MakersAsylumIndia/IS2026_SU_Team13_Vector/Documentation/Block Diagram.jpeg

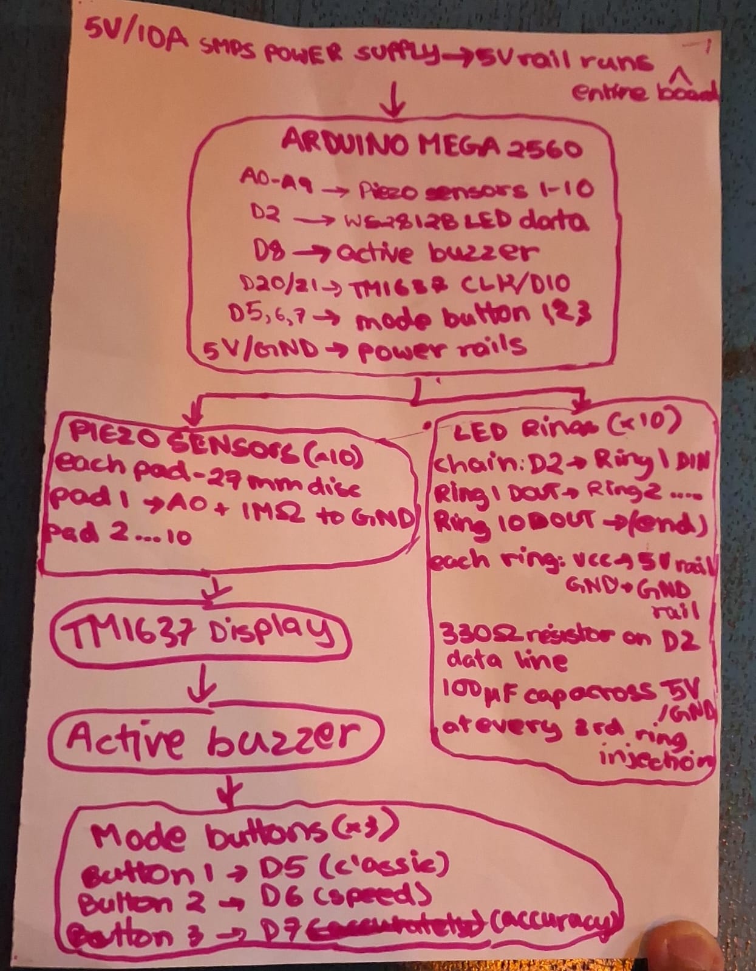
Documentation/Block Diagram.jpeg
