MakersAsylumIndia/IS2026_SU_Team13_Vector/Documentation/Project_Ideation_Sketch.jpeg

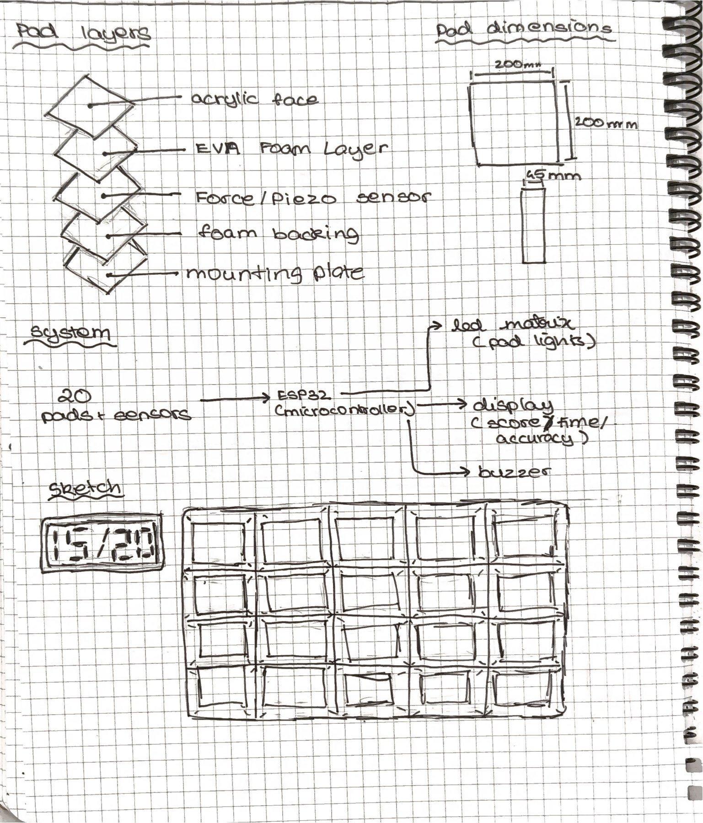
Documentation/Project_Ideation_Sketch.jpeg
