MakersAsylumIndia/IS2026_SU_Team13_Vector/Photos_Videos/Images/shared image (18).jpeg

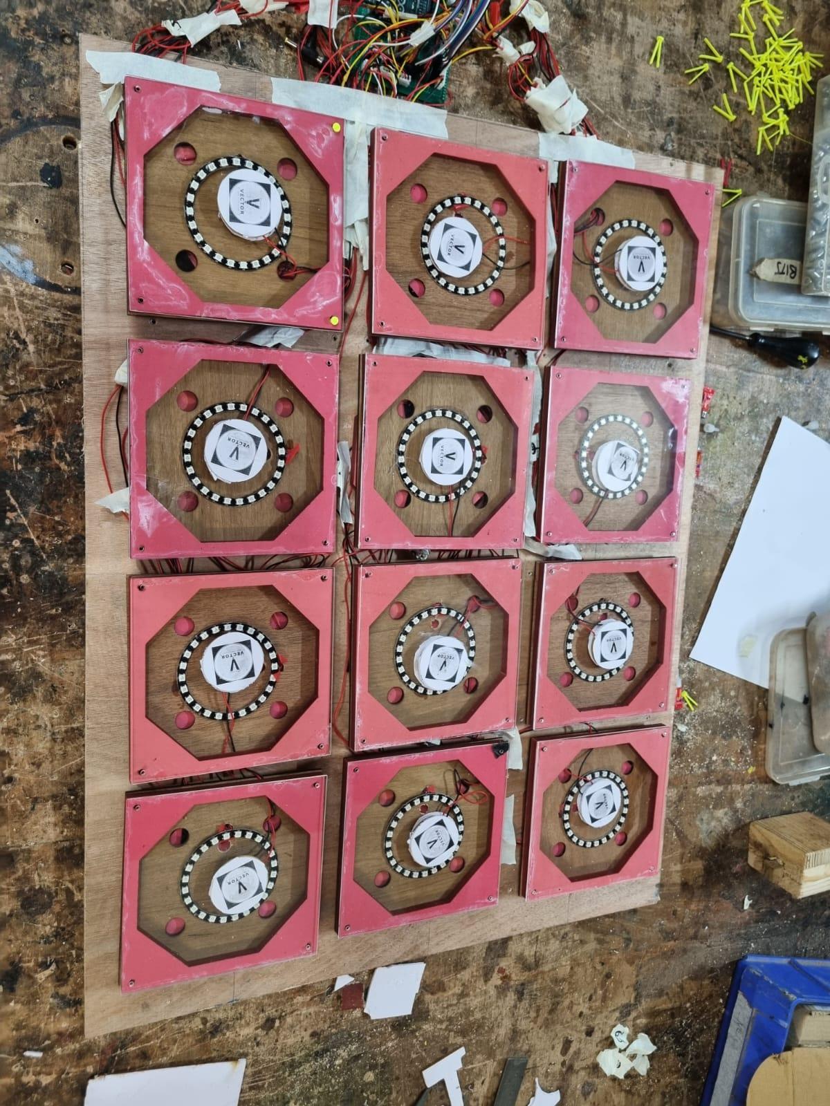
Photos_Videos/Images/shared image (18).jpeg
