MakersAsylumIndia/IS2026_SU_Team13_Vector/Photos_Videos/Images/Team_Vector_01.jpg

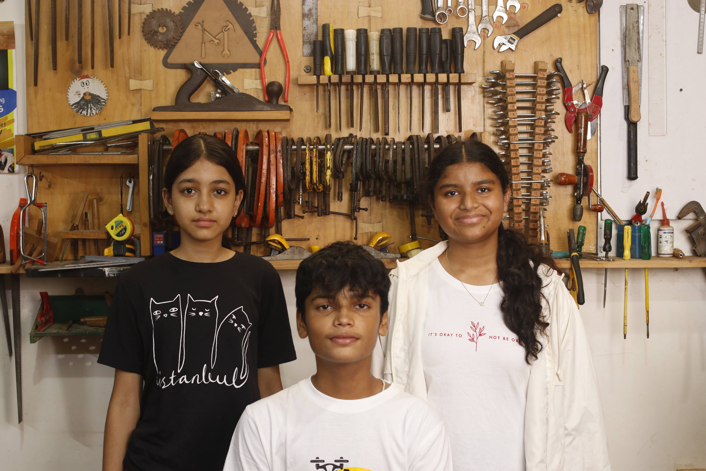
Photos_Videos/Images/Team_Vector_01.jpg
