MakersAsylumIndia/IS2026_SU_Team13_Vector/Photos_Videos/Images/Team_Vector_03.jpg

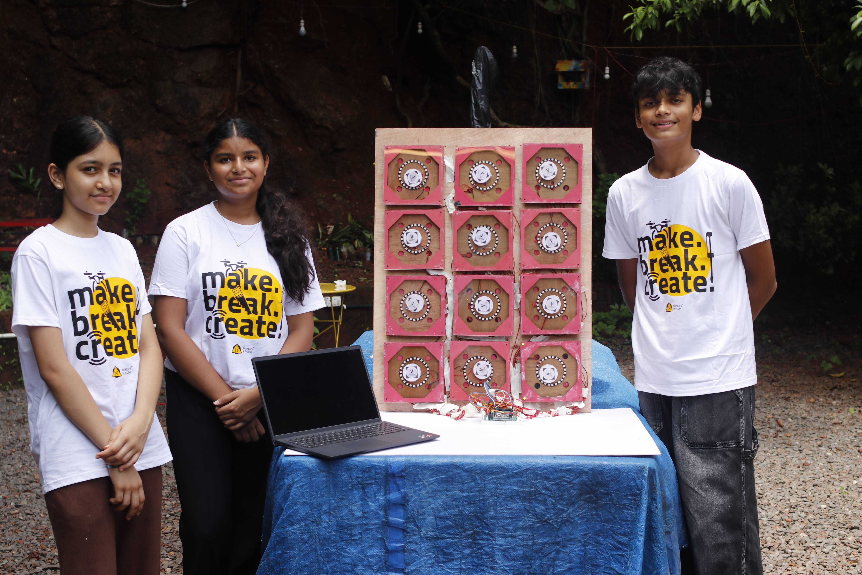
Photos_Videos/Images/Team_Vector_03.jpg
