MakersAsylumIndia/IS2026_SU_Team13_Vector/Photos_Videos/Images/Team_Vector_04.jpg

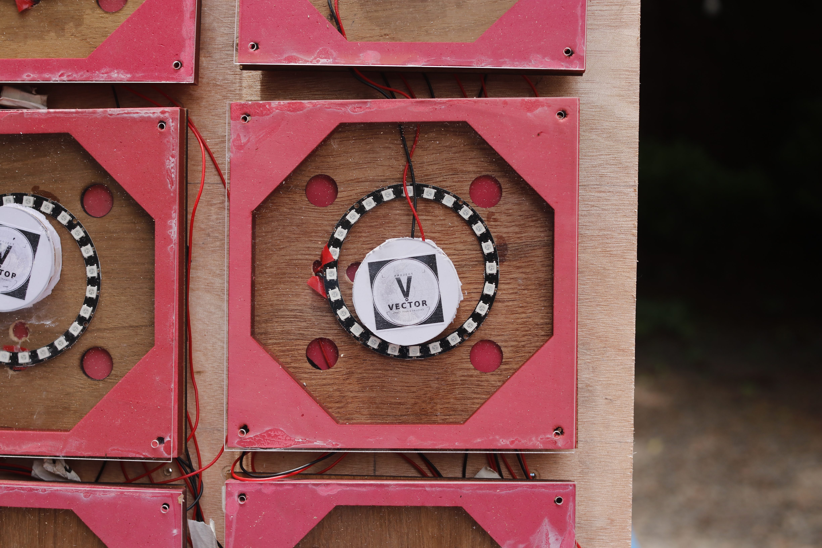
Photos_Videos/Images/Team_Vector_04.jpg
