MakersAsylumIndia/IS2026_SU_Team13_Vector/Photos_Videos/Images/WhatsApp Image 2026-06-22 at 17.43.26 (1).jpeg

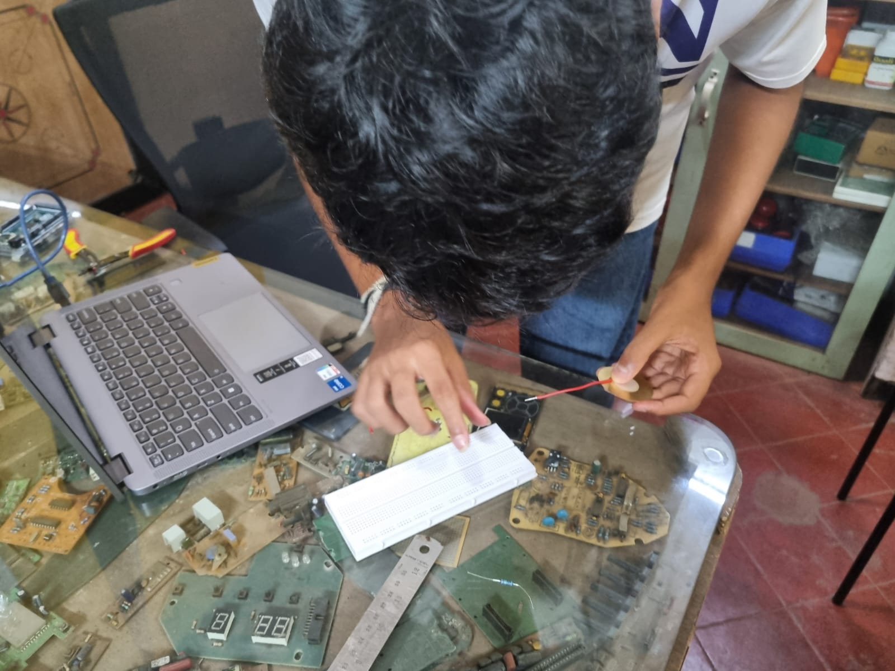
Photos_Videos/Images/WhatsApp Image 2026-06-22 at 17.43.26 (1).jpeg
