MakersAsylumIndia/IS2026_SU_Team13_Vector/Photos_Videos/Images/WhatsApp Image 2026-06-23 at 19.54.47 (3).jpeg

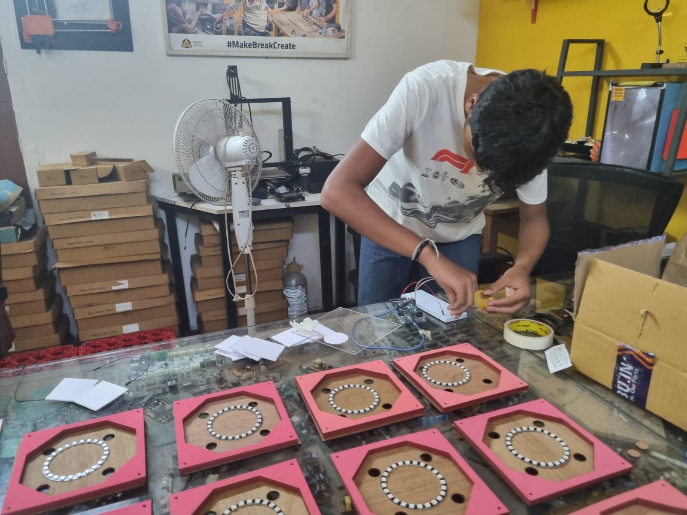
Photos_Videos/Images/WhatsApp Image 2026-06-23 at 19.54.47 (3).jpeg
