MakersAsylumIndia/IS2026_SU_Team13_Vector/Photos_Videos/Images/WhatsApp Image 2026-06-24 at 16.36.41.jpeg

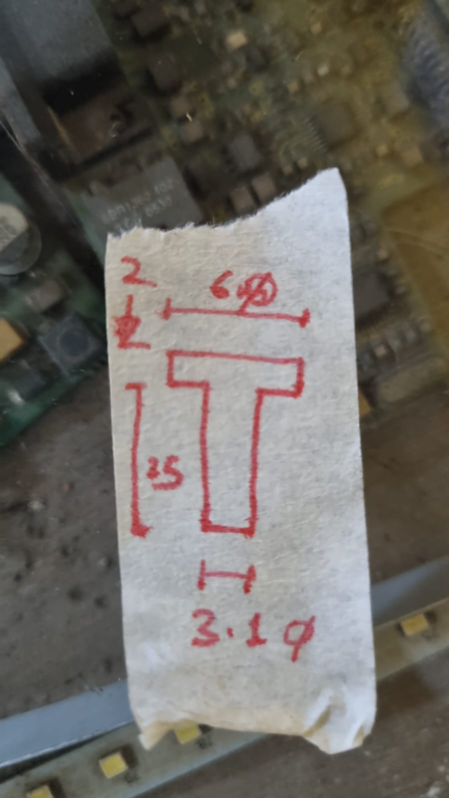
Photos_Videos/Images/WhatsApp Image 2026-06-24 at 16.36.41.jpeg
