MakersAsylumIndia/IS2026_SU_Team13_Vector/Photos_Videos/Images/WhatsApp Image 2026-06-24 at 21.34.04 (1).jpeg

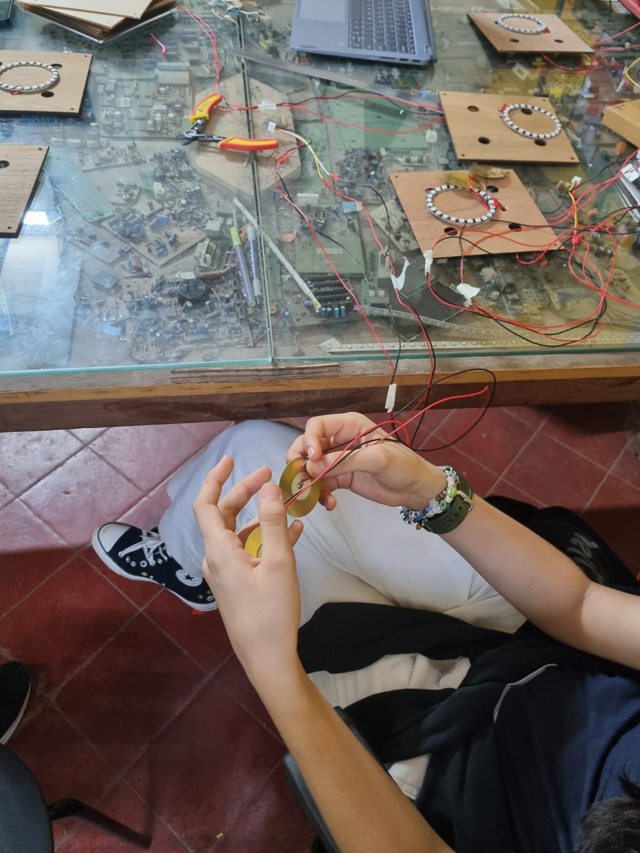
Photos_Videos/Images/WhatsApp Image 2026-06-24 at 21.34.04 (1).jpeg
