MakersAsylumIndia/IS2026_SU_Team13_Vector/Photos_Videos/Images/WhatsApp Image 2026-06-25 at 19.44.05 (2).jpeg

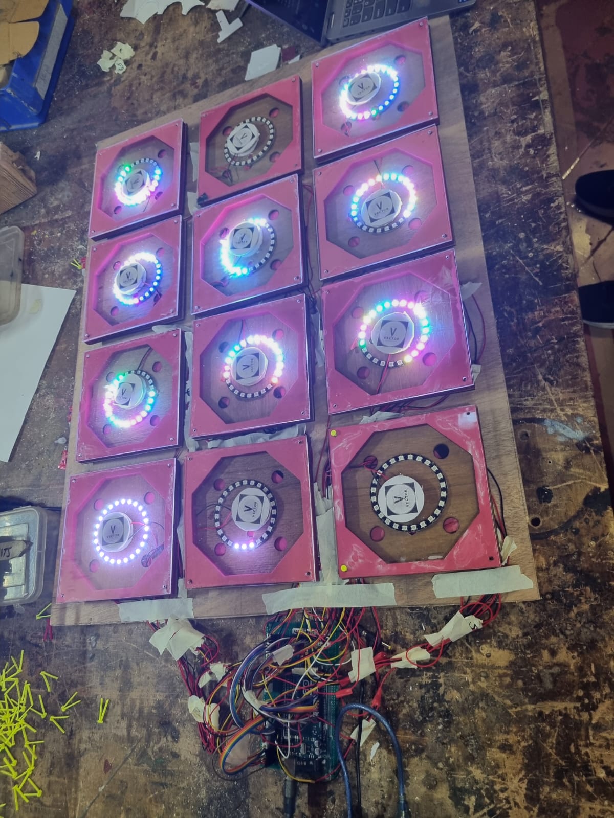
Photos_Videos/Images/WhatsApp Image 2026-06-25 at 19.44.05 (2).jpeg
